iamericmin/Time-Machine-Mk.-8/TM8-firmware/scratchpad/bme680test/bme680test.ino

/***************************************************************************
  This is a library for the BME680 gas, humidity, temperature & pressure sensor

  Designed specifically to work with the Adafruit BME680 Breakout
  ----> http://www.adafruit.com/products/3660

  These sensors use I2C or SPI to communicate, 2 or 4 pins are required
  to interface.

  Adafruit invests time and resources providing this open source code,
  please support Adafruit and open-source hardware by purchasing products
  from Adafruit!

  Written by Limor Fried & Kevin Townsend for Adafruit Industries.
  BSD license, all text above must be included in any redistribution
 ***************************************************************************/

#include <Wire.h>
#include "wiring_private.h"
#include <Adafruit_Sensor.h>
#include "Adafruit_BME680.h"

#define SEALEVELPRESSURE_HPA (1013.25)

TwoWire wire1(&sercom2, 4, 3); // new Wire object to set up second I2C port on SERCOM 2

Adafruit_BME680 bme = Adafruit_BME680(&wire1); // I2C

void setup() {

  Wire.begin();
  wire1.begin();

  pinPeripheral(4, PIO_SERCOM); // SDA: D4 / PA08
  pinPeripheral(3, PIO_SERCOM); // SCL: D3 / PA09
  
  Serial.begin(9600);
  while (!Serial);
  Serial.println(F("BME680 test"));

  if (!bme.begin(0x76)) {
    Serial.print("Made it here 1");
    Serial.println("Could not find a valid BME680 sensor, check wiring!");
    while (1);
  }
}

void loop() {
  if (! bme.performReading()) {
    Serial.println("Failed to perform reading :(");
    return;
  }
  Serial.print("Temperature = ");
  Serial.print(bme.temperature);
  Serial.println(" *C");

  Serial.print("Pressure = ");
  Serial.print(bme.pressure / 100.0);
  Serial.println(" hPa");

  Serial.print("Humidity = ");
  Serial.print(bme.humidity);
  Serial.println(" %");

  Serial.print("Gas = ");
  Serial.print(bme.gas_resistance / 1000.0);
  Serial.println(" KOhms");

  Serial.print("Approx. Altitude = ");
  Serial.print(bme.readAltitude(SEALEVELPRESSURE_HPA));
  Serial.println(" m");

  Serial.println();
  delay(2000);
}
